JX5S/Talnet-STM32-console/Priklady/99. Hry/Snake/include/graphics.h

static const unsigned short apple[]  = {
  0x6de6, 0x6de6, 0x6de6, 0x6de6, 0x6de6, 0x4127, 0x6de6, 0x6de6, 
  0x6de6, 0x6de6, 0x6de6, 0x6de6, 0x4127, 0x6de6, 0x6de6, 0x6de6, 
  0x6de6, 0xa986, 0xa986, 0xa986, 0x4127, 0xa986, 0xa986, 0x6de6, 
  0xa986, 0xa986, 0xa986, 0xa986, 0xa986, 0xa986, 0xa986, 0xa986, 
  0xa986, 0xa986, 0xa986, 0xa986, 0xa986, 0xa986, 0xa986, 0xa986, 
  0xa986, 0xa986, 0xa986, 0xa986, 0xa986, 0xa986, 0xa986, 0xa986, 
  0x6de6, 0xa986, 0xa986, 0xa986, 0xa986, 0xa986, 0xa986, 0x6de6, 
  0x6de6, 0x6de6, 0xa986, 0x6de6, 0x6de6, 0xa986, 0x6de6, 0x6de6
};

static const unsigned short Bent_apple01[]  = {
  0x6de6, 0x6de6, 0x61c6, 0x61c6, 0x8aa7, 0x61c6, 0x6de6, 0x6de6, 
  0x6de6, 0x6de6, 0x61c6, 0x61c6, 0x4127, 0x61c6, 0x61c6, 0x6de6, 
  0x6de6, 0x61c6, 0x4127, 0x4127, 0x61c6, 0x8aa7, 0x61c6, 0x61c6, 
  0x6de6, 0x61c6, 0x61c6, 0x8aa7, 0x8aa7, 0x61c6, 0x4127, 0x61c6, 
  0x6de6, 0x61c6, 0x61c6, 0x61c6, 0x4127, 0x4127, 0x61c6, 0x8aa7, 
  0x6de6, 0x6de6, 0x61c6, 0x61c6, 0x61c6, 0x61c6, 0x61c6, 0x61c6, 
  0x6de6, 0x6de6, 0x6de6, 0x61c6, 0x61c6, 0x61c6, 0x6de6, 0x6de6, 
  0x6de6, 0x6de6, 0x6de6, 0x6de6, 0x6de6, 0x6de6, 0x6de6, 0x6de6
};

static const unsigned short Bent_apple03[]  = {
  0x6de6, 0x6de6, 0x61c6, 0x61c6, 0x8aa7, 0x61c6, 0x6de6, 0x6de6, 
  0x6de6, 0x61c6, 0x61c6, 0x4127, 0x61c6, 0x61c6, 0x6de6, 0x6de6, 
  0x61c6, 0x61c6, 0x8aa7, 0x61c6, 0x4127, 0x61c6, 0x61c6, 0x6de6, 
  0x8aa7, 0x4127, 0x61c6, 0x8aa7, 0x4127, 0x61c6, 0x61c6, 0x6de6, 
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
  0x6de6, 0x6de6, 0x6de6, 0x61c6, 0x8aa7, 0x6de6, 0x6de6, 0x6de6, 
  0x6de6, 0x6de6, 0x6de6, 0x4127, 0x61c6, 0x6de6, 0x6de6, 0x6de6, 
  0x6de6, 0x6de6, 0x61c6, 0x61c6, 0x4127, 0x61c6, 0x6de6, 0x6de6, 
  0x6de6, 0x6de6, 0x61c6, 0x8aa7, 0x61c6, 0x61c6, 0x6de6, 0x6de6
};

static const unsigned short Tail3[]  = {
  0x6de6, 0x6de6, 0x6de6, 0x6de6, 0x6de6, 0x6de6, 0x6de6, 0x6de6, 
  0x6de6, 0x6de6, 0x6de6, 0x6de6, 0x6de6, 0x6de6, 0x6de6, 0x6de6, 
  0x61c6, 0x61c6, 0x6de6, 0x6de6, 0x6de6, 0x6de6, 0x6de6, 0x6de6, 
  0x8aa7, 0x61c6, 0x4127, 0x61c6, 0x61c6, 0x6de6, 0x6de6, 0x6de6, 
  0x61c6, 0x4127, 0x61c6, 0x8aa7, 0x61c6, 0x6de6, 0x6de6, 0x6de6, 
  0x61c6, 0x61c6, 0x6de6, 0x6de6, 0x6de6, 0x6de6, 0x6de6, 0x6de6, 
  0x6de6, 0x6de6, 0x6de6, 0x6de6, 0x6de6, 0x6de6, 0x6de6, 0x6de6, 
  0x6de6, 0x6de6, 0x6de6, 0x6de6, 0x6de6, 0x6de6, 0x6de6, 0x6de6
};
